nataliethenerd/CGB_ReverseEngineer/schematic/kicad schematic/CGB_IR.kicad_sch

## KiCad design schematic/kicad schematic/CGB_IR.kicad_sch (2024-07-14, last stored version)

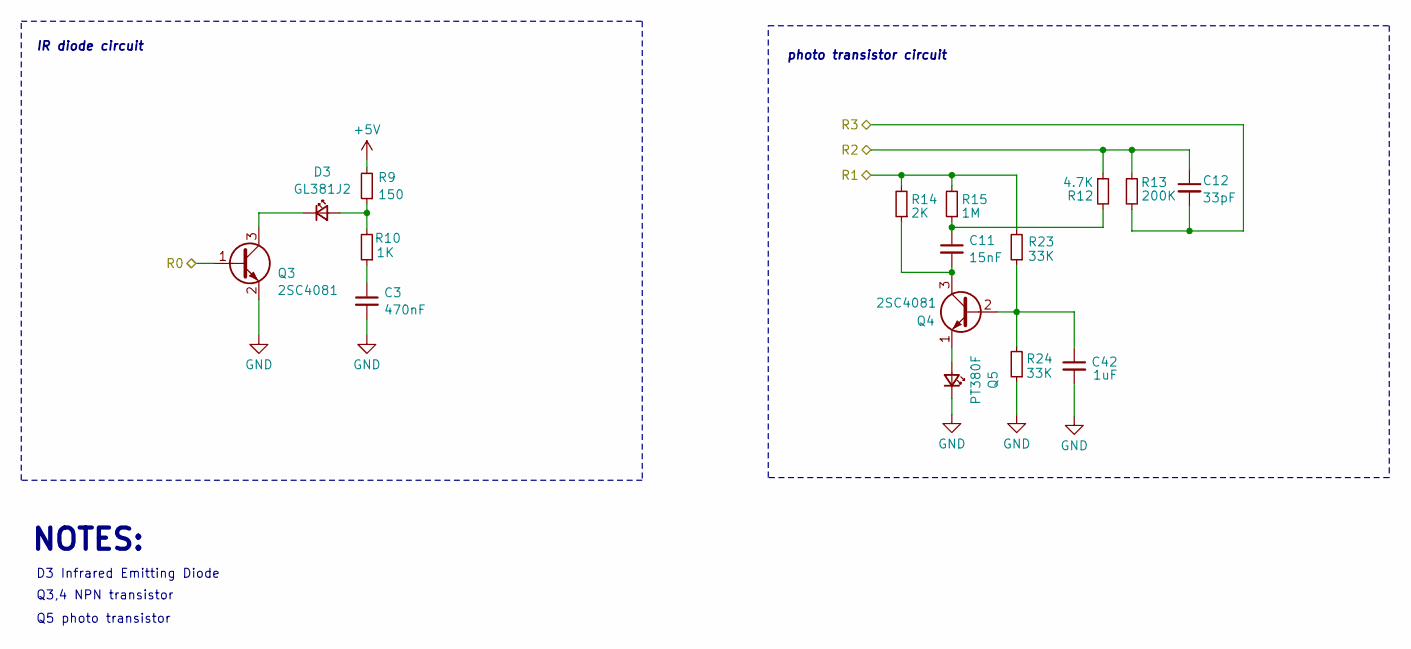
[picture p9: schematic CGB_IR.kicad_sch]

Parts:
C3: 470nF; C_0603_1608Metric
C11: 15nF; C_0603_1608Metric
C12: 33pF; C_0603_1608Metric
C42: 1uF; C_0603_1608Metric
D3: GL381J2
Q3, Q4: 2SC4081; SOT-323_SC-70
Q5: PT380F
R9: 150; R_0603_1608Metric
R10: 1K; R_0603_1608Metric
R12: 4.7K; R_0603_1608Metric
R13: 200K; R_0603_1608Metric
R14: 2K; R_0603_1608Metric
R15: 1M; R_0603_1608Metric
R23, R24: 33K; R_0603_1608Metric

Connections:
+5V: R9.2
GND: C3.2, C42.2, Q3.2 (B), Q5.1 (K), R24.1
unnamed: C3.1, R10.1
unnamed: C11.1, R12.2, R15.1
unnamed: C11.2, Q4.3 (C), R14.1
unnamed: C42.1, Q4.2 (B), R23.1, R24.2
unnamed: D3.1 (K), Q3.3 (C)
unnamed: D3.2 (A), R9.1, R10.2
unnamed: Q4.1 (E), Q5.2 (A)
R0: Q3.1 (E)
R1: R14.2, R15.2, R23.2
R2: C12.1, R12.1, R13.1
R3: C12.2, R13.2

Notes on the sheet:
D3 Infrared Emitting Diode
IR diode circuit
photo transistor circuit
NOTES:
Q5 photo transistor
Q3,4 NPN transistor
