nataliethenerd/CGB_ReverseEngineer/schematic/kicad schematic/CGB_Serial.kicad_sch

## KiCad design schematic/kicad schematic/CGB_Serial.kicad_sch (2024-07-14, last stored version)

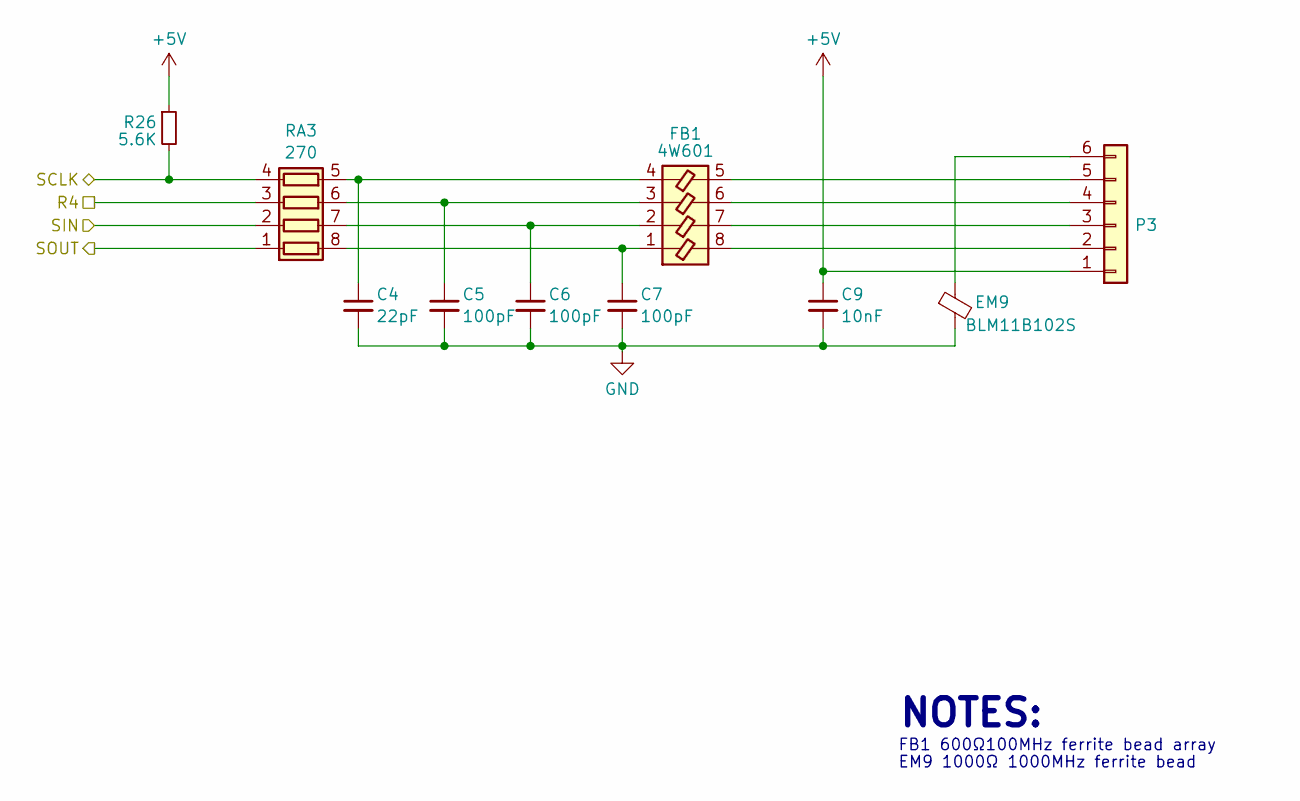
[picture p10: schematic CGB_Serial.kicad_sch]

Parts:
C4: 22pF; C_0603_1608Metric
C5, C6, C7: 100pF; C_0603_1608Metric
C9: 10nF; C_0603_1608Metric
EM9: BLM11B102S; R_0603_1608Metric
FB1: 4W601; R_Array_Concave_4x0603
P3: Conn_01x06; Serial CGB
R26: 5.6K; R_0603_1608Metric
RA3: 270; R_Array_Concave_4x0603

Connections:
+5V: C9.1, P3.1, R26.1
GND: C4.2, C5.2, C6.2, C7.2, C9.2, EM9.2
unnamed: C4.1, FB1.4, RA3.5 (R4.2)
unnamed: C5.1, FB1.3, RA3.6 (R3.2)
unnamed: C6.1, FB1.2, RA3.7 (R2.2)
unnamed: C7.1, FB1.1, RA3.8 (R1.2)
unnamed: EM9.1, P3.6
unnamed: FB1.5, P3.5
unnamed: FB1.6, P3.4
unnamed: FB1.7, P3.3
unnamed: FB1.8, P3.2
R4: RA3.3 (R3.1)
SCLK: R26.2, RA3.4 (R4.1)
SIN: RA3.2 (R2.1)
SOUT: RA3.1 (R1.1)

Notes on the sheet:
EM9 1000Ω 1000MHz ferrite bead
FB1 600Ω100MHz ferrite bead array
NOTES:
