nataliethenerd/CGB_ReverseEngineer/schematic/kicad schematic/CGB_Sound.kicad_sch

## KiCad design schematic/kicad schematic/CGB_Sound.kicad_sch (2024-07-14, last stored version)

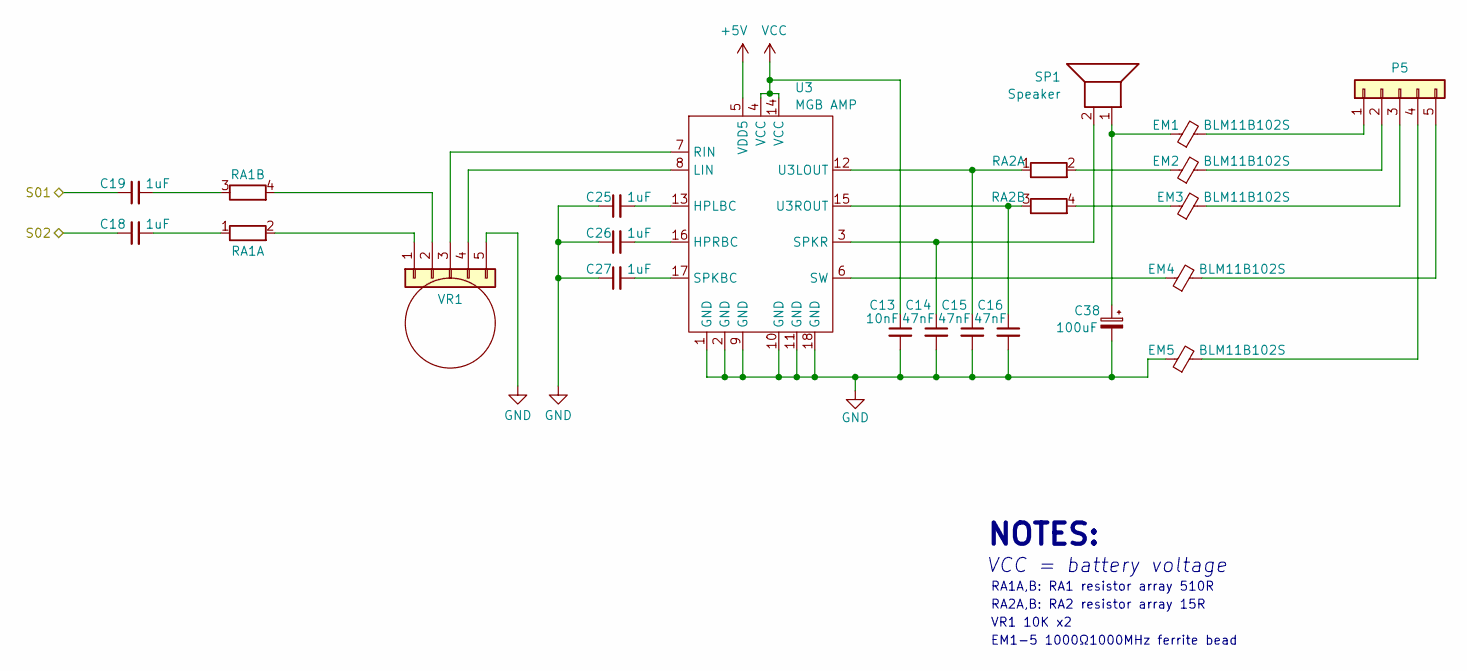
[picture p11: schematic CGB_Sound.kicad_sch]

Parts:
C13: 10nF; C_0603_1608Metric
C14, C15, C16: 47nF; C_0603_1608Metric
C18, C19, C25, C26, C27: 1uF; C_0603_1608Metric
C38: 100uF; CP_Elec_5x5.3
EM1, EM2, EM3, EM4, EM5: BLM11B102S; R_0603_1608Metric
P5: Conn_01x05; HPjack
RA1, RA2: R_Pack02_SIP_Split; R_Array_Concave_2x0603
SP1: Speaker; TestPoint_2Pads_Pitch2.54mm_Drill0.8mm
U3: MGB AMP; Amp MGB
VR1: Conn_01x05; Volume wheel CGB

Connections:
+5V: U3.5 (VDD5)
GND: C13.2, C14.2, C15.2, C16.2, C25.1, C26.1, C27.1, C38.2, EM5.1, U3.1 (GND), U3.2 (GND), U3.9 (GND), U3.10 (GND), U3.11 (GND), U3.18 (GND), VR1.5
unnamed: C14.1, SP1.2, U3.3 (SPKR)
unnamed: C15.1, RA2.1 (R1.1), U3.12 (U3LOUT)
unnamed: C16.1, RA2.3 (R2.1), U3.15 (U3ROUT)
unnamed: C18.2, RA1.1 (R1.1)
unnamed: C19.2, RA1.3 (R2.1)
unnamed: C25.2, U3.13 (HPLBC)
unnamed: C26.2, U3.16 (HPRBC)
unnamed: C27.2, U3.17 (SPKBC)
unnamed: C38.1, EM1.1, SP1.1
unnamed: EM1.2, P5.1
unnamed: EM2.1, RA2.2 (R1.2)
unnamed: EM2.2, P5.2
unnamed: EM3.1, RA2.4 (R2.2)
unnamed: EM3.2, P5.3
unnamed: EM4.1, U3.6 (SW)
unnamed: EM4.2, P5.5
unnamed: EM5.2, P5.4
unnamed: RA1.2 (R1.2), VR1.1
unnamed: RA1.4 (R2.2), VR1.2
unnamed: U3.7 (RIN), VR1.3
unnamed: U3.8 (LIN), VR1.4
S01: C19.1
S02: C18.1
VCC: C13.1, U3.4 (VCC), U3.14 (VCC)

Notes on the sheet:
EM1-5 1000Ω1000MHz ferrite bead
RA1A,B: RA1 resistor array 510R
VR1 10K x2
VCC = battery voltage
NOTES:
RA2A,B: RA2 resistor array 15R
