nataliethenerd/CGB_ReverseEngineer/schematic/kicad schematic/cgb_controls.kicad_sch

## KiCad design schematic/kicad schematic/cgb_controls.kicad_sch (2024-07-14, last stored version)

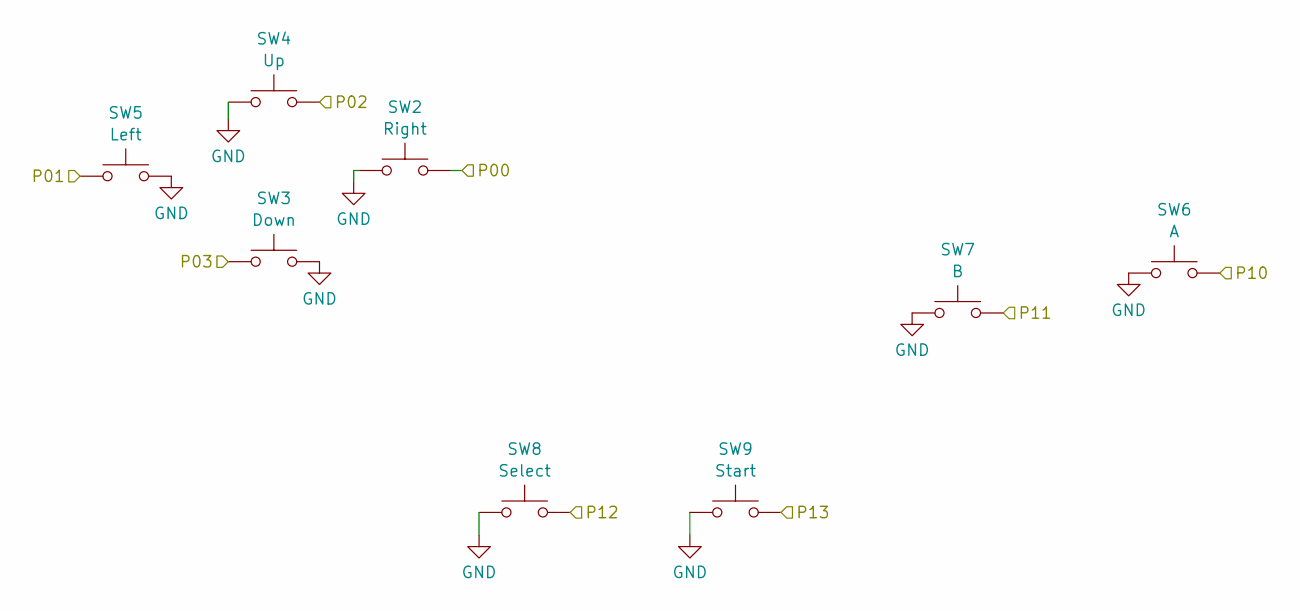
[picture p12: schematic cgb_controls.kicad_sch]

Parts:
SW2: Right; Dpad CGB
SW3: Down; Dpad CGB
SW4: Up; Dpad CGB
SW5: Left; Dpad CGB
SW6: A; AB CGB
SW7: B; AB CGB
SW8: Select; Select CGB
SW9: Start; Start CGB

Connections:
GND: SW2.1, SW3.2, SW4.1, SW5.2, SW6.1, SW7.1, SW8.1, SW9.1
P00: SW2.2
P01: SW5.1
P02: SW4.2
P03: SW3.1
P10: SW6.2
P11: SW7.2
P12: SW8.2
P13: SW9.2
