nataliethenerd/CGB_ReverseEngineer/schematic/kicad schematic/cgb_power.kicad_sch

## KiCad design schematic/kicad schematic/cgb_power.kicad_sch (2024-07-14, last stored version)

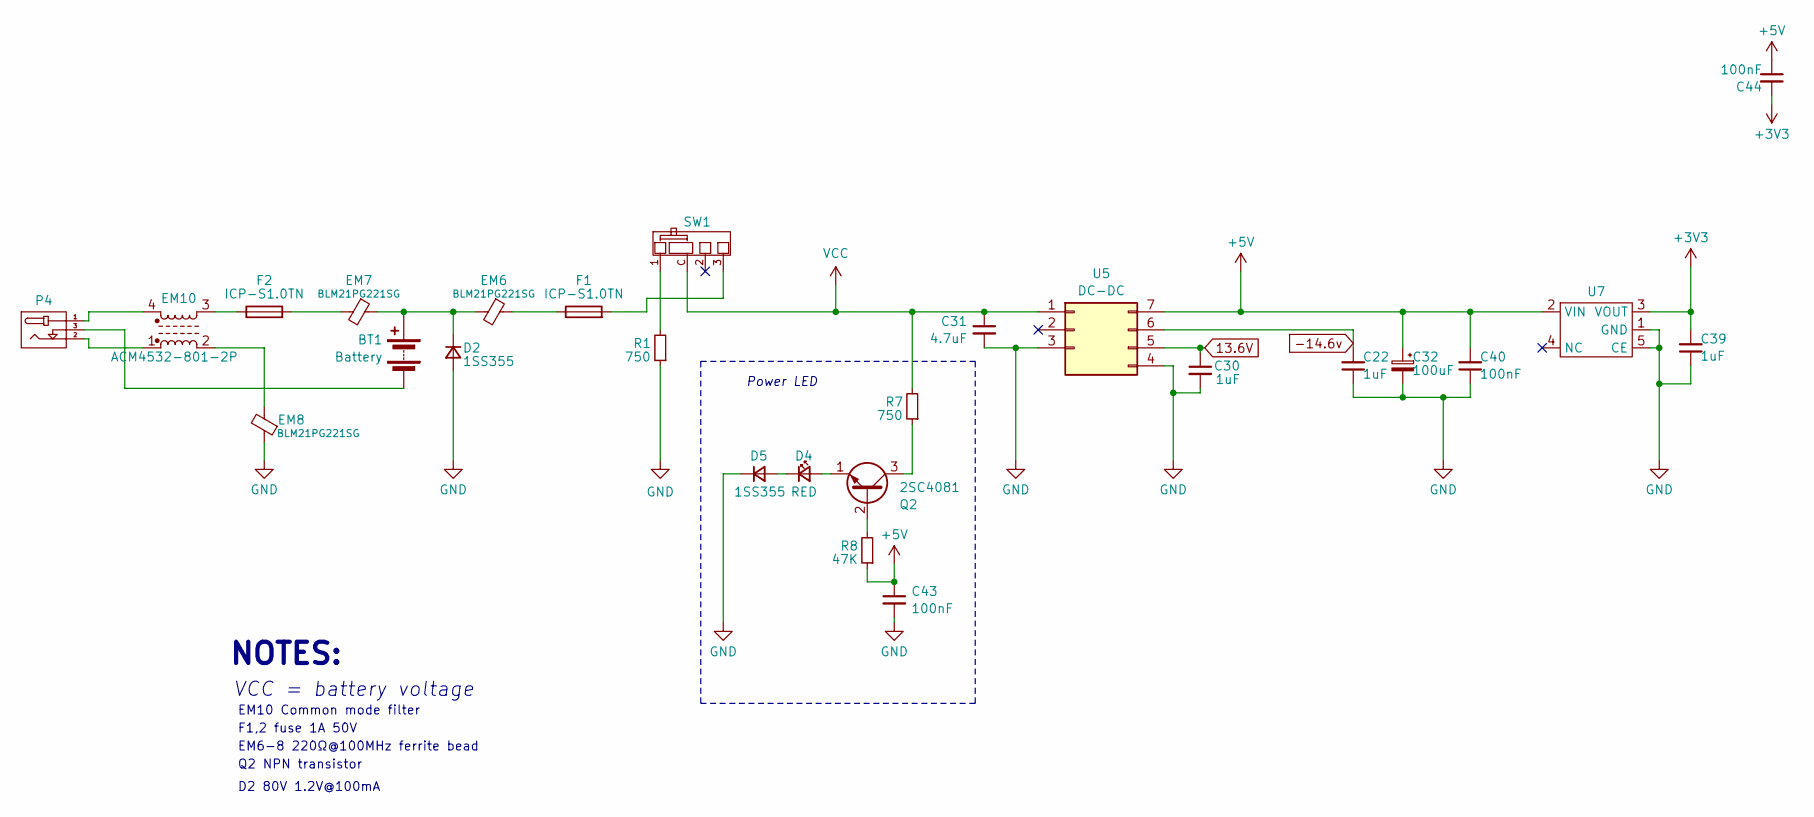
[picture p13: schematic cgb_power.kicad_sch]

Parts:
BT1: Battery; Battery CGB
C22, C30, C39: 1uF; C_0603_1608Metric
C31: 4.7uF; C_0603_1608Metric
C32: 100uF; CP_Elec_6.3x5.4
C40, C43, C44: 100nF; C_0603_1608Metric
D2, D5: 1SS355; D_SOD-323_HandSoldering
D4: RED; LED_D3.0mm
EM6, EM7, EM8: BLM21PG221SG; R_0805_2012Metric
EM10: ACM4532-801-2P; Crystal_SMD_EuroQuartz_MJ-4Pin_5.0x3.2mm
F1, F2: ICP-S1.0TN; Fuse_1206_3216Metric_Pad1.42x1.75mm_HandSolder
P4: DCJACK
Q2: 2SC4081; SOT-323_SC-70
R1, R7: 750; R_0603_1608Metric
R8: 47K; R_0603_1608Metric
SW1: Switch CGB
U5: DC-DC; DC
U7: SOT-23-5

Connections:
13.6V: C30.1, U5.5
+3V3: C39.2, C44.2, U7.3 (VOUT)
+5V: C32.1, C40.2, C43.1, C44.1, R8.1, U5.7, U7.2 (VIN)
-14.6v: C22.2, U5.6
GND: C22.1, C30.2, C31.2, C32.2, C39.1, C40.1, C43.2, D2.2 (A), D5.1 (K), EM8.1, R1.1, U5.3, U5.4, U7.1 (GND), U7.5 (CE)
unnamed: BT1.1 (+), D2.1 (K), EM6.2, EM7.1
unnamed: BT1.2 (-), P4.3
unnamed: D4.1 (K), D5.2 (A)
unnamed: D4.2 (A), Q2.1 (B)
unnamed: EM6.1, F1.1
unnamed: EM7.2, F2.2
unnamed: EM10.1, P4.2
unnamed: EM8.2, EM10.2
unnamed: EM10.3, F2.1
unnamed: EM10.4, P4.1
unnamed: F1.2, SW1.3
unnamed: Q2.2, R8.2
unnamed: Q2.3 (E), R7.1
unnamed: R1.2, SW1.1
VCC: C31.1, R7.2, SW1.C, U5.1

Notes on the sheet:
NOTES:
D2 80V 1.2V@100mA
EM6-8 220Ω@100MHz ferrite bead
EM10 Common mode filter
F1,2 fuse 1A 50V
Power LED
Q2 NPN transistor
VCC = battery voltage
