nataliethenerd/CGB_ReverseEngineer/schematic/kicad schematic/cgb_screen.kicad_sch

## KiCad design schematic/kicad schematic/cgb_screen.kicad_sch (2024-07-14, last stored version)

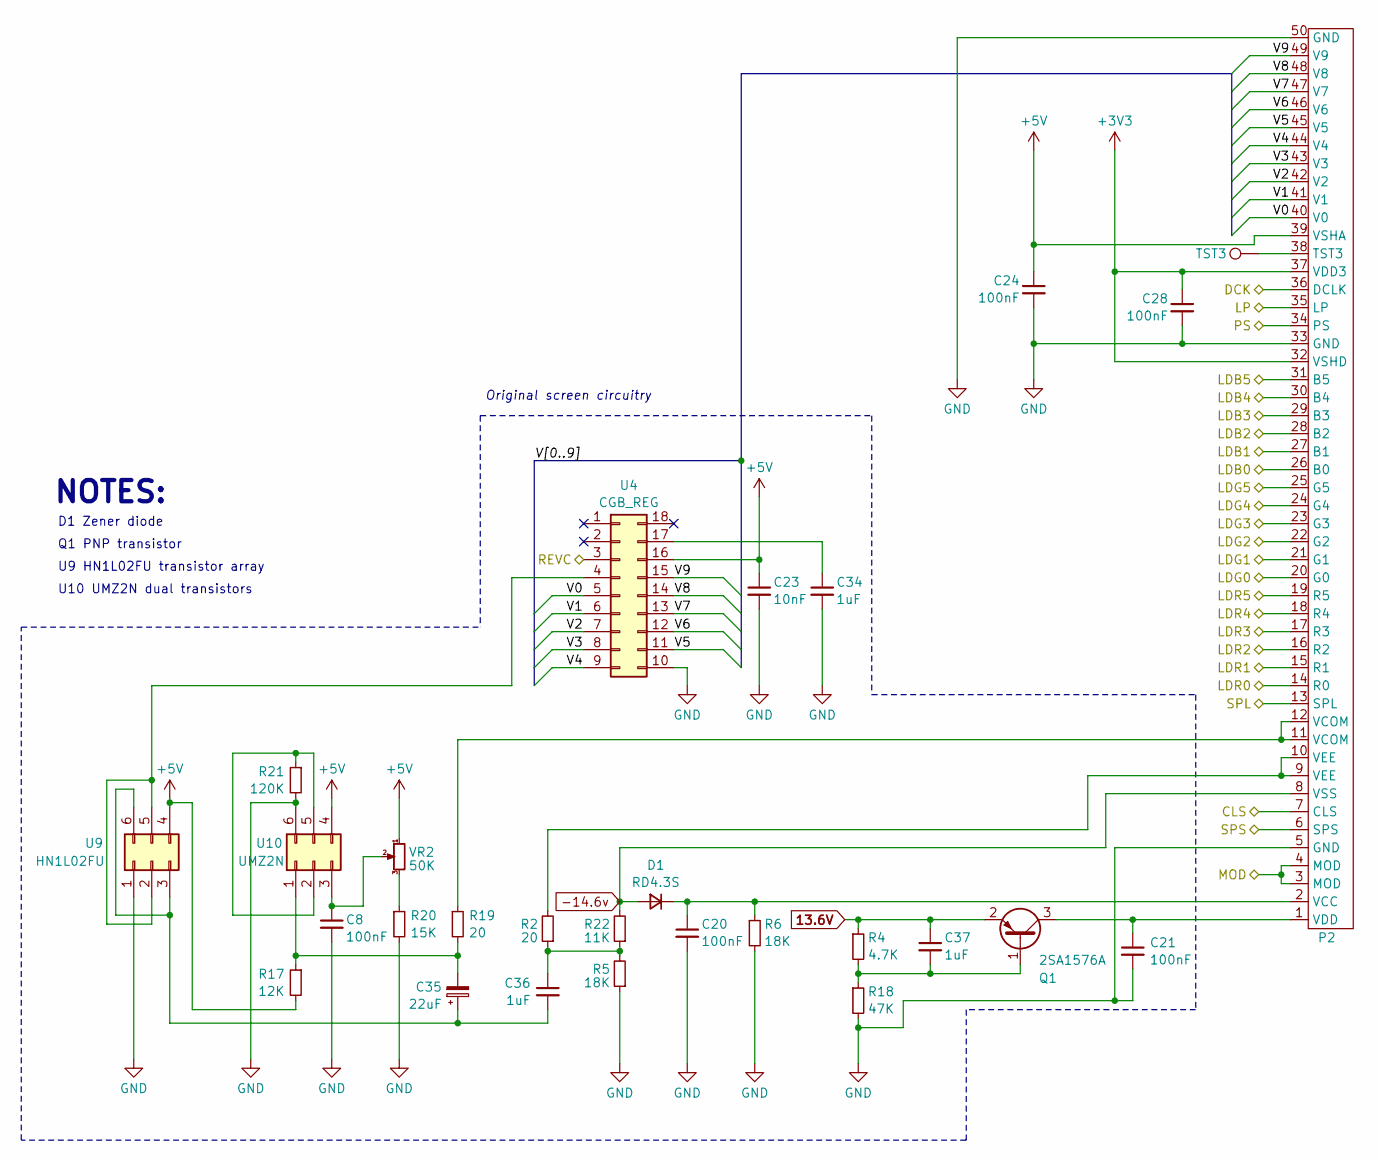
[picture p14: schematic cgb_screen.kicad_sch]

Parts:
C8, C20, C21, C24, C28: 100nF; C_0603_1608Metric
C23: 10nF; C_0603_1608Metric
C34, C36, C37: 1uF; C_0603_1608Metric
C35: 22uF; CP_Elec_4x3.9
D1: RD4.3S; D_SOD-323_HandSoldering
P2: Screen CGB
Q1: 2SA1576A; SOT-323_SC-70
R2, R19: 20; R_0603_1608Metric
R4: 4.7K; R_0603_1608Metric
R5, R6: 18K; R_0603_1608Metric
R17: 12K; R_0603_1608Metric
R18: 47K; R_0603_1608Metric
R20: 15K; R_0603_1608Metric
R21: 120K; R_0603_1608Metric
R22: 11K; R_0603_1608Metric
TST3: TestPoint
U4: CGB_REG; Reg CGB
U9: HN1L02FU; SOT-363_SC-70-6
U10: UMZ2N; SOT-363_SC-70-6
VR2: 50K

Connections:
13.6V: C37.1, Q1.2 (C), R4.1
+3V3: C28.1, P2.32 (VSHD), P2.37 (VDD3)
+5V: C23.1, C24.1, P2.39 (VSHA), R17.2, U4.16, U9.4, U10.4, VR2.1
-14.6v: D1.2 (A), P2.8 (VSS), R22.2
CLS: P2.7 (CLS)
DCK: P2.36 (DCLK)
GND: C8.2, C20.2, C21.2, C23.2, C24.2, C28.2, C34.2, P2.5 (GND), P2.33 (GND), P2.50 (GND), R5.1, R6.2, R18.2, R20.2, R21.2, U4.10, U9.1, U10.6
LDB0: P2.26 (B0)
LDB1: P2.27 (B1)
LDB2: P2.28 (B2)
LDB3: P2.29 (B3)
LDB4: P2.30 (B4)
LDB5: P2.31 (B5)
LDG0: P2.20 (G0)
LDG1: P2.21 (G1)
LDG2: P2.22 (G2)
LDG3: P2.23 (G3)
LDG4: P2.24 (G4)
LDG5: P2.25 (G5)
LDR0: P2.14 (R0)
LDR1: P2.15 (R1)
LDR2: P2.16 (R2)
LDR3: P2.17 (R3)
LDR4: P2.18 (R4)
LDR5: P2.19 (R5)
LP: P2.35 (LP)
MOD: P2.3 (MOD), P2.4 (MOD)
unnamed: C8.1, U10.3, VR2.2
unnamed: C20.1, D1.1 (K), P2.2 (VCC), R6.1
unnamed: C21.1, P2.1 (VDD), Q1.3 (B)
unnamed: C34.1, U4.17
unnamed: C35.1, C36.2, U9.3, U9.6
unnamed: C35.2, R17.1, R19.2, U10.1
unnamed: C36.1, R2.1, R5.2, R22.1
unnamed: C37.2, Q1.1 (E), R4.2, R18.1
unnamed: P2.9 (VEE), P2.10 (VEE), R2.2
unnamed: P2.11 (VCOM), P2.12 (VCOM), R19.1
unnamed: P2.38 (TST3), TST3.1
unnamed: R20.1, VR2.3
unnamed: R21.1, U10.2, U10.5
unnamed: U4.4, U9.2, U9.5
PS: P2.34 (PS)
REVC: U4.3
SPL: P2.13 (SPL)
SPS: P2.6 (SPS)
V0: P2.40 (V0), U4.5
V1: P2.41 (V1), U4.6
V2: P2.42 (V2), U4.7
V3: P2.43 (V3), U4.8
V4: P2.44 (V4), U4.9
V5: P2.45 (V5), U4.11
V6: P2.46 (V6), U4.12
V7: P2.47 (V7), U4.13
V8: P2.48 (V8), U4.14
V9: P2.49 (V9), U4.15

Notes on the sheet:
U9 HN1L02FU transistor array
D1 Zener diode
Q1 PNP transistor
Original screen circuitry
NOTES:
U10 UMZ2N dual transistors
