nataliethenerd/CGB_ReverseEngineer/schematic/kicad schematic/gbc.kicad_sch

## KiCad design schematic/kicad schematic/gbc.kicad_sch (2024-07-14, last stored version)

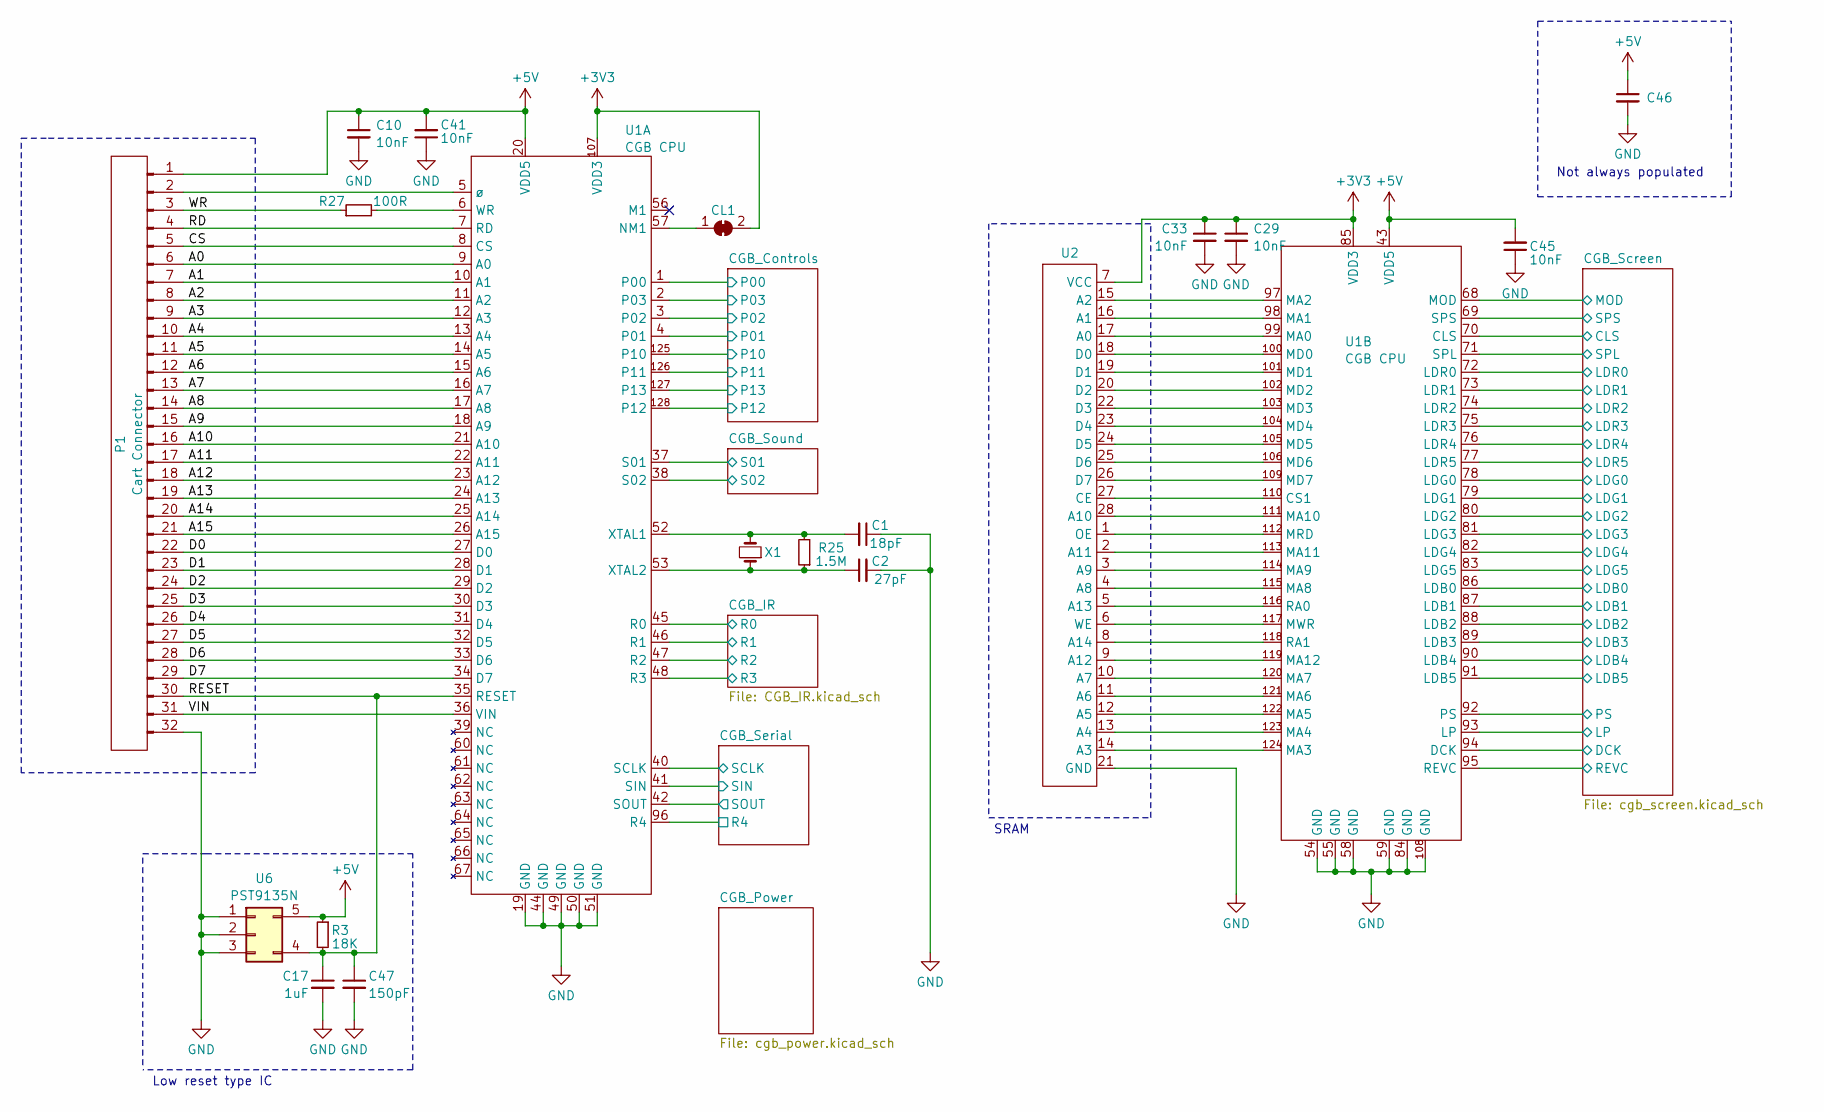
[picture p15: schematic gbc.kicad_sch]

Parts:
C1: 18pF; C_0603_1608Metric
C2: 27pF; C_0603_1608Metric
C10, C29, C33, C41, C45: 10nF; C_0603_1608Metric
C17: 1uF; C_0603_1608Metric
C46: C_0603_1608Metric
C47: 150pF; C_0603_1608Metric
CL1: SolderJumper_2_Bridged; SolderJumper-2_P1.3mm_Bridged_Pad1.0x1.5mm
P1: Cart Connector; Cart CGB
R3: 18K; R_0603_1608Metric
R25: 1.5M; R_0603_1608Metric
R27: 100R; R_0603_1608Metric
U1: CGB CPU; CPU CGB
U2: TSOP-I-28_11.8x8mm_P0.55mm
U6: PST9135N; SOT-23-5
X1: Crystal_Small; Crystal CGB

Connections:
+3V3: C29.1, C33.1, CL1.2 (B), U1.85 (VDD3), U1.107 (VDD3), U2.7 (VCC)
+5V: C10.1, C41.2, C45.2, C46.1, P1.1, R3.1, U1.20 (VDD5), U1.43 (VDD5), U6.5
A0: P1.6, U1.9 (A0)
A1: P1.7, U1.10 (A1)
A2: P1.8, U1.11 (A2)
A3: P1.9, U1.12 (A3)
A4: P1.10, U1.13 (A4)
A5: P1.11, U1.14 (A5)
A6: P1.12, U1.15 (A6)
A7: P1.13, U1.16 (A7)
A8: P1.14, U1.17 (A8)
A9: P1.15, U1.18 (A9)
A10: P1.16, U1.21 (A10)
A11: P1.17, U1.22 (A11)
A12: P1.18, U1.23 (A12)
A13: P1.19, U1.24 (A13)
A14: P1.20, U1.25 (A14)
A15: P1.21, U1.26 (A15)
CLS: U1.70 (CLS)
CS: P1.5, U1.8 (CS)
D0: P1.22, U1.27 (D0)
D1: P1.23, U1.28 (D1)
D2: P1.24, U1.29 (D2)
D3: P1.25, U1.30 (D3)
D4: P1.26, U1.31 (D4)
D5: P1.27, U1.32 (D5)
D6: P1.28, U1.33 (D6)
D7: P1.29, U1.34 (D7)
DCK: U1.94 (DCK)
GND: C1.1, C2.2, C10.2, C17.2, C29.2, C33.2, C41.1, C45.1, C46.2, C47.2, P1.32, U1.19 (GND), U1.44 (GND), U1.49 (GND), U1.50 (GND), U1.51 (GND), U1.54 (GND), U1.55 (GND), U1.58 (GND), U1.59 (GND), U1.84 (GND), U1.108 (GND), U2.21 (GND), U6.1, U6.2, U6.3
LDB0: U1.86 (LDB0)
LDB1: U1.87 (LDB1)
LDB2: U1.88 (LDB2)
LDB3: U1.89 (LDB3)
LDB4: U1.90 (LDB4)
LDB5: U1.91 (LDB5)
LDG0: U1.78 (LDG0)
LDG1: U1.79 (LDG1)
LDG2: U1.80 (LDG2)
LDG3: U1.81 (LDG3)
LDG4: U1.82 (LDG4)
LDG5: U1.83 (LDG5)
LDR0: U1.72 (LDR0)
LDR1: U1.73 (LDR1)
LDR2: U1.74 (LDR2)
LDR3: U1.75 (LDR3)
LDR4: U1.76 (LDR4)
LDR5: U1.77 (LDR5)
LP: U1.93 (LP)
MOD: U1.68 (MOD)
unnamed: C1.2, R25.2, U1.52 (XTAL1), X1.2
unnamed: C2.1, R25.1, U1.53 (XTAL2), X1.1
unnamed: CL1.1 (A), U1.57 (NMI)
unnamed: P1.2, U1.5 (ø)
unnamed: R27.2, U1.6 (WR)
unnamed: U1.97 (MA2), U2.15 (A2)
unnamed: U1.98 (MA1), U2.16 (A1)
unnamed: U1.99 (MA0), U2.17 (A0)
unnamed: U1.100 (MD0), U2.18 (D0)
unnamed: U1.101 (MD1), U2.19 (D1)
unnamed: U1.102 (MD2), U2.20 (D2)
unnamed: U1.103 (MD3), U2.22 (D3)
unnamed: U1.104 (MD4), U2.23 (D4)
unnamed: U1.105 (MD5), U2.24 (D5)
unnamed: U1.106 (MD6), U2.25 (D6)
unnamed: U1.109 (MD7), U2.26 (D7)
unnamed: U1.110 (CS1), U2.27 (CE)
unnamed: U1.111 (MA10), U2.28 (A10)
unnamed: U1.112 (MRD), U2.1 (OE)
unnamed: U1.113 (MA11), U2.2 (A11)
unnamed: U1.114 (MA9), U2.3 (A9)
unnamed: U1.115 (MA8), U2.4 (A8)
unnamed: U1.116 (RA0), U2.5 (A13)
unnamed: U1.117 (MWR), U2.6 (WE)
unnamed: U1.118 (RA1), U2.8 (A14)
unnamed: U1.119 (MA12), U2.9 (A12)
unnamed: U1.120 (MA7), U2.10 (A7)
unnamed: U1.121 (MA6), U2.11 (A6)
unnamed: U1.122 (MA5), U2.12 (A5)
unnamed: U1.123 (MA4), U2.13 (A4)
unnamed: U1.124 (MA3), U2.14 (A3)
P00: U1.1 (P00)
P01: U1.4 (P01)
P02: U1.3 (P02)
P03: U1.2 (P03)
P10: U1.125 (P10)
P11: U1.126 (P11)
P12: U1.128 (P13)
P13: U1.127 (P12)
PS: U1.92 (PS)
R0: U1.45 (R0)
R1: U1.46 (R1)
R2: U1.47 (R2)
R3: U1.48 (R3)
R4: U1.96 (R4)
RD: P1.4, U1.7 (RD)
RESET: C17.1, C47.1, P1.30, R3.2, U1.35 (RESET), U6.4
REVC: U1.95 (REVC)
S01: U1.37 (S01)
S02: U1.38 (S02)
SCLK: U1.40 (SCLK)
SIN: U1.41 (SIN)
SOUT: U1.42 (SOUT)
SPL: U1.71 (SPL)
SPS: U1.69 (SPS)
VIN: P1.31, U1.36 (VIN)
WR: P1.3, R27.1

Notes on the sheet:
Not always populated
Low reset type IC
SRAM
